yu2924/SensorClock/firmware/main/modules/DataLogger.cpp

//
//  DataLogger.cpp
//  SensorClock
//
//  created by yu2924 on 2026-04-15
//

#include "DataLogger.h"

#include <algorithm>
#include <cassert>
#include <cmath>
#include <ctime>
#include <mutex>
#include "utilities/platform.h"
#include "utilities/xheap.h"
#include "modules/BoardFs.h"
#include "modules/Dispatcher.h"

namespace fcc
{
	static constexpr uint32_t fccFromStr(const char(&sz)[5])
	{
		return sz[3] * 0x1000000u + sz[2] * 0x10000u + sz[1] * 0x100u + sz[0];
	}
	static constexpr std::array<char, 5> strFromFcc(uint32_t fcc)
	{
		return std::array<char, 5>{ (char)(fcc), (char)(fcc >> 8), (char)(fcc >> 16), (char)(fcc >> 24), 0 };
	}
};

template<typename ExtRecordT, typename IntRecordT, typename ISnapshot, size_t BufferSize, uint32_t Signature, uint32_t Version> struct HistoryBufferBaseT
{
	struct FileHeader
	{
		uint32_t sig;
		uint32_t ver;
		uint32_t wlen;
		uint32_t reserved;
	};
	static constexpr size_t TotalBytes = BufferSize * sizeof(IntRecordT);
	IntRecordT* bufferPtr = nullptr;
	uint32_t whead = 0, wlen = 0;
	std::recursive_mutex mtx;
	HistoryBufferBaseT()
	{
		bufferPtr = (IntRecordT*)xheap::memAlloc(TotalBytes);
		if(!bufferPtr) { DEBUGPRINTW("HistoryBuffer(%s): malloc(%zu) failed", fcc::strFromFcc(Signature).data(), TotalBytes); }
	}
	~HistoryBufferBaseT()
	{
		xheap::memFree(bufferPtr);
	}
	size_t getNumRecordsInternal() const
	{
		return wlen;
	}
	IntRecordT& getRecordAtInternal(size_t idx) const
	{
		assert(bufferPtr && (idx < wlen));
		int rhead = (int)whead - (int)wlen + (int)idx; if(rhead < 0) { rhead += BufferSize; }
		return bufferPtr[rhead];
	}
	void reset()
	{
		std::lock_guard sl(mtx);
		whead = wlen = 0;
	}
	bool load(const char* path)
	{
		auto loadproc = [this](FILE* pf)->bool
		{
			FileHeader hdr{};
			if(fread(&hdr, 1, sizeof(hdr), pf) != sizeof(hdr)) { return false; }
			if((hdr.sig != Signature) || (hdr.ver != Version) || (BufferSize < hdr.wlen)) { return false; }
			for(size_t c = hdr.wlen, i = 0; i < c; ++i)
			{
				IntRecordT& rec = bufferPtr[i];
				if(fread(&rec, 1, sizeof(IntRecordT), pf) != sizeof(IntRecordT)) { return false; }
			}
			whead = wlen = hdr.wlen;
			if(BufferSize <= whead) { whead = 0; }
			DEBUGPRINTI("HistoryBuffer(%s): load %zu records", fcc::strFromFcc(Signature).data(), wlen);
			return true;
		};
		std::lock_guard sl(mtx);
		if(!bufferPtr) { return false; }
		bool r = false;
		if(FILE* pf = fopen(path, "rb"))
		{
			r = loadproc(pf);
			fclose(pf);
		}
		if(!r) { reset(); }
		return r;
	}
	bool save(const char* path)
	{
		auto saveproc = [this](FILE* pf)->bool
		{
			FileHeader hdr = { Signature, Version, wlen, 0 };
			if(fwrite(&hdr, 1, sizeof(hdr), pf) != sizeof(hdr)) { return false; }
			for(size_t c = wlen, i = 0; i < c; ++i)
			{
				const IntRecordT& rec = getRecordAtInternal(i);
				if(fwrite(&rec, 1, sizeof(IntRecordT), pf) != sizeof(IntRecordT)) { return false; }
			}
			DEBUGPRINTI("HistoryBuffer(%s): save %zu records", fcc::strFromFcc(Signature).data(), wlen);
			return true;
		};
		std::lock_guard sl(mtx);
		if(!bufferPtr) { return false; }
		bool r = false;
		if(FILE* pf = fopen(path, "wb"))
		{
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
